ArqueologiaDigital/SintetizadorGuidoStolfi/1974_12_26__Relatorio_No.1_JJN_e_Eloah/originais/pagina_05f.tiff

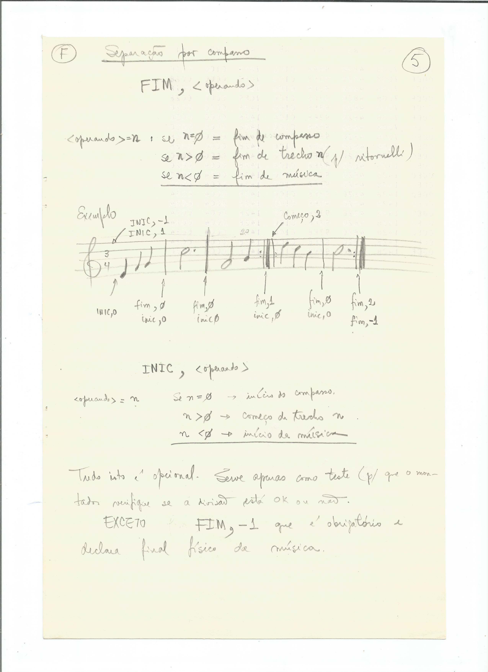
1974_12_26__Relatorio_No.1_JJN_e_Eloah/originais/pagina_05f.tiff
