ArqueologiaDigital/SintetizadorGuidoStolfi/1979__Descrição_de_um_Sistema_Modular__Guido_Stolfi/original_pages/pagina_05.png

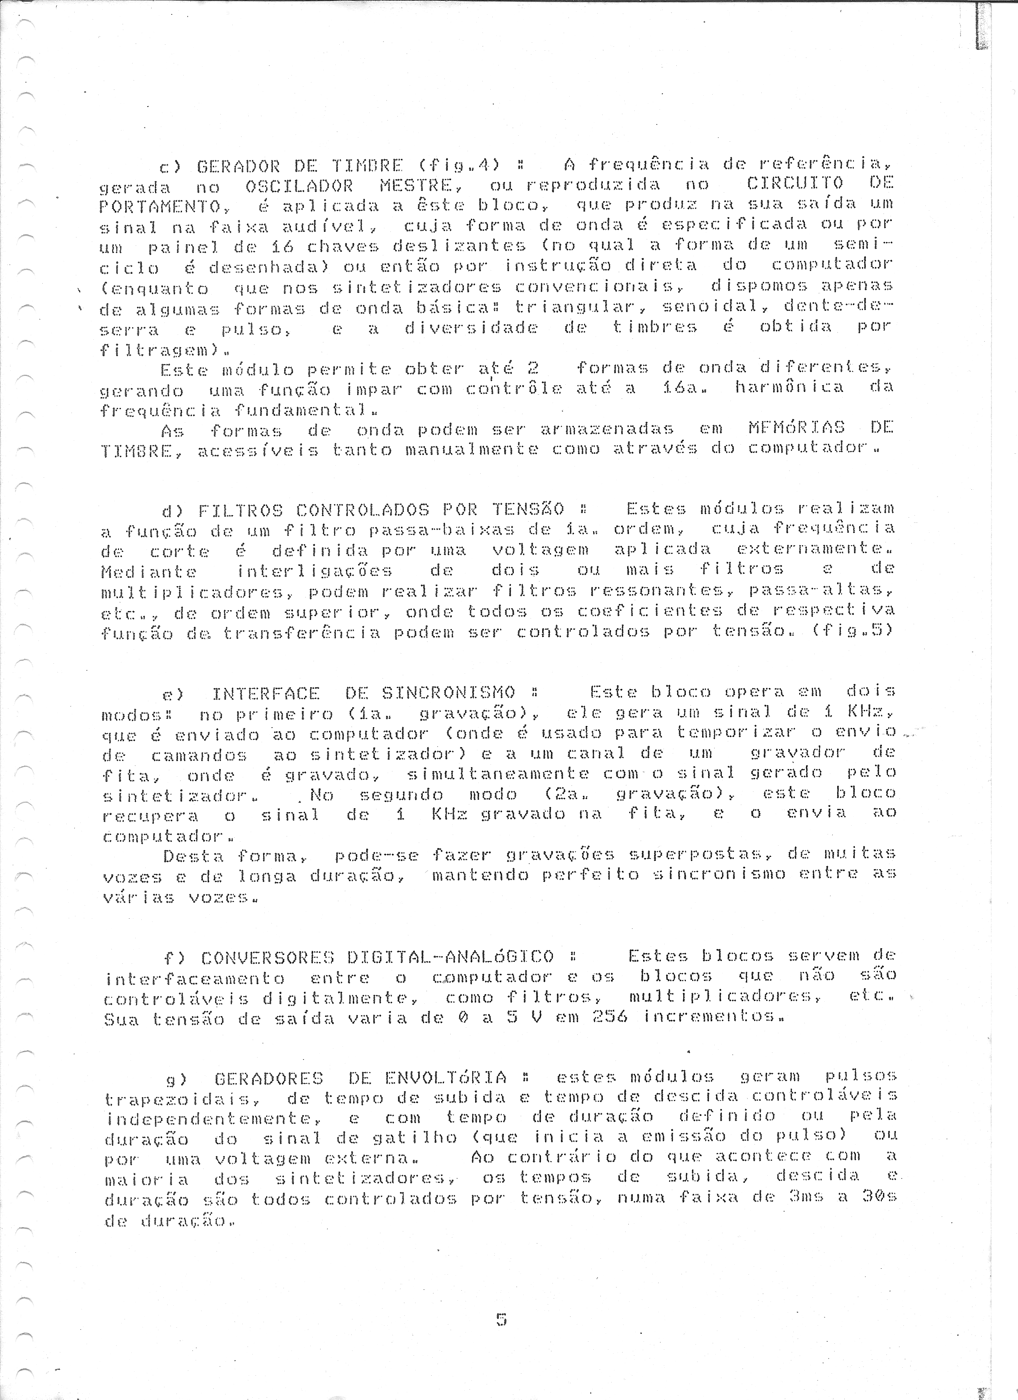
1979__Descrição_de_um_Sistema_Modular__Guido_Stolfi/original_pages/pagina_05.png
