ArqueologiaDigital/SintetizadorGuidoStolfi/fotolitos/INTF_SINCR/interface_de_recepcao/rect2.png

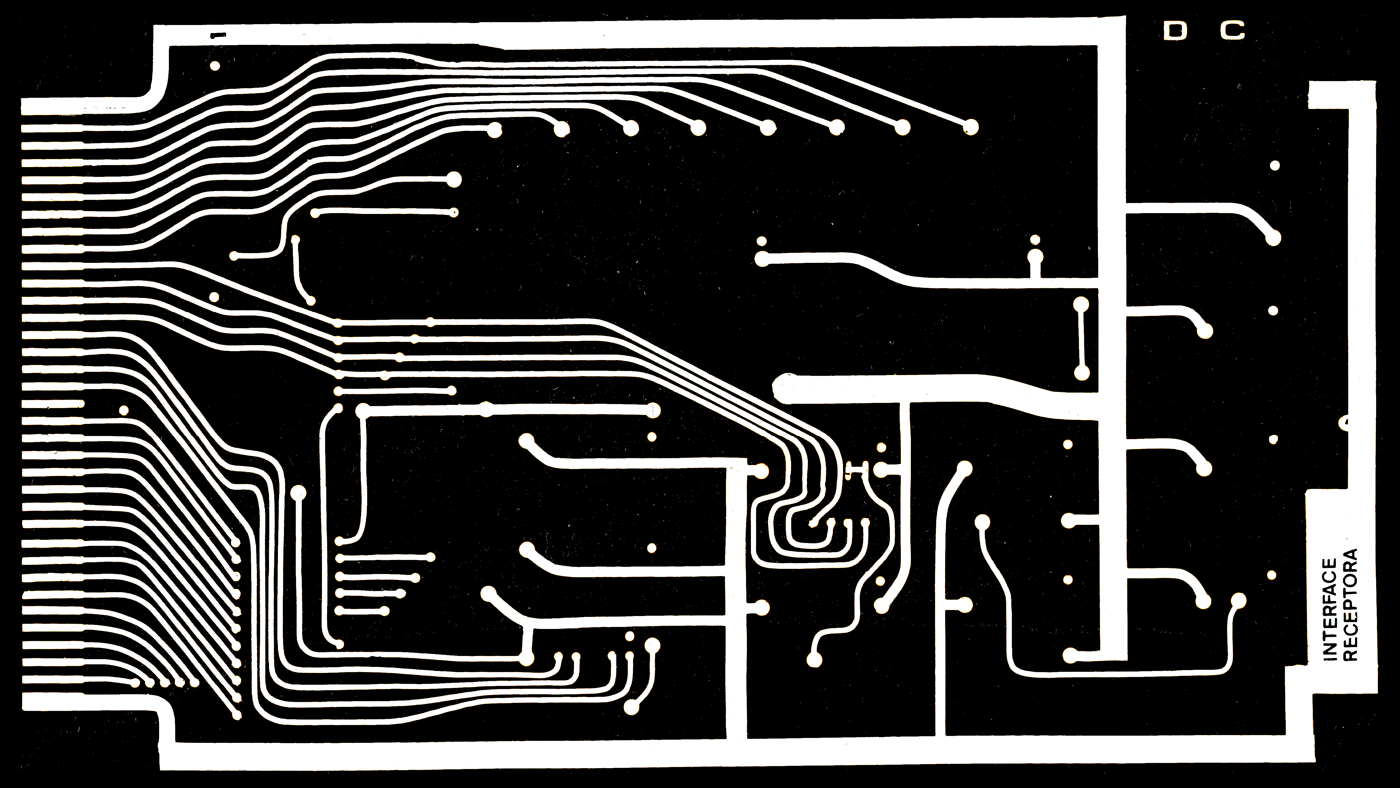
fotolitos/INTF_SINCR/interface_de_recepcao/rect2.png
