ArqueologiaDigital/SintetizadorGuidoStolfi/Programa_de_Codificação_de_uma_Partitura/originais/paginas_01.jpg

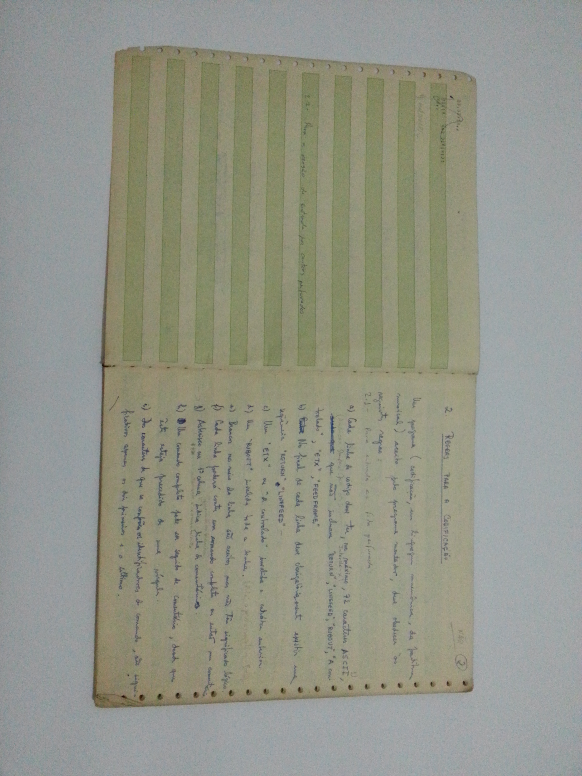
Programa_de_Codificação_de_uma_Partitura/originais/paginas_01.jpg
