ArqueologiaDigital/SintetizadorGuidoStolfi/Programa_de_Codificação_de_uma_Partitura/originais/paginas_20.jpg

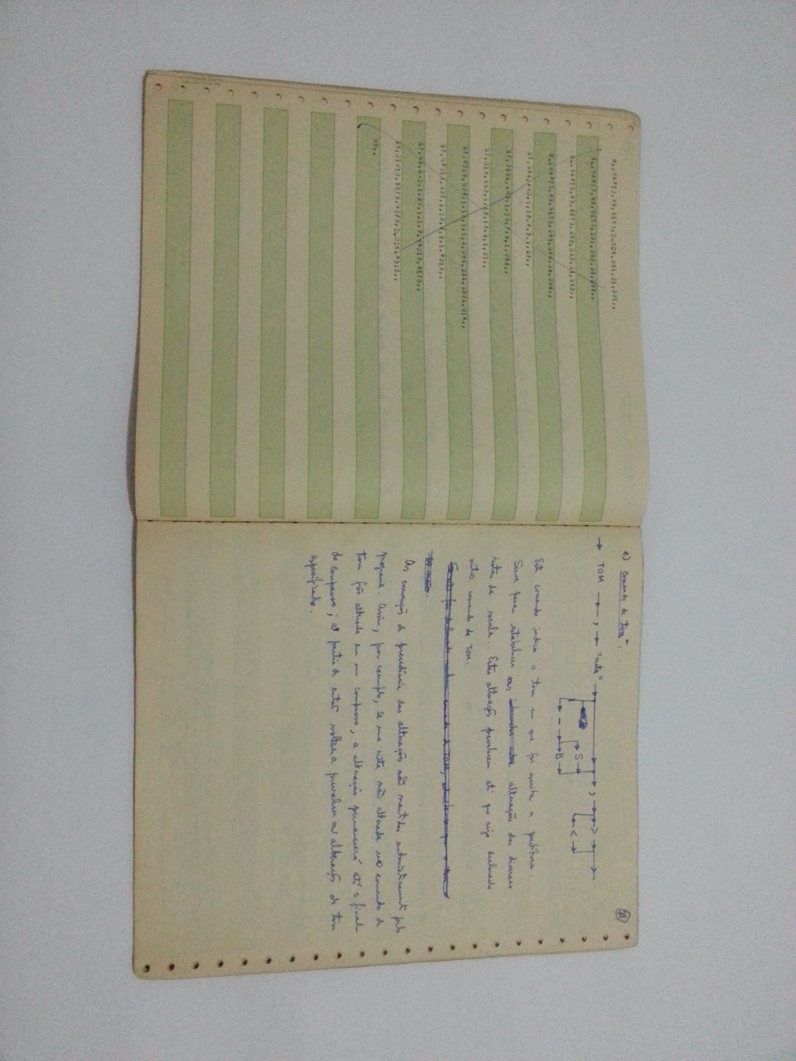
Programa_de_Codificação_de_uma_Partitura/originais/paginas_20.jpg
